Ibrahim-El-Khalil-Chaida/Real-Time-Embedded-System-for-Signal-Optimization-in-Battery-Analysis/Hardware/Images/Fritzing images/Current 2 pcb.JPG

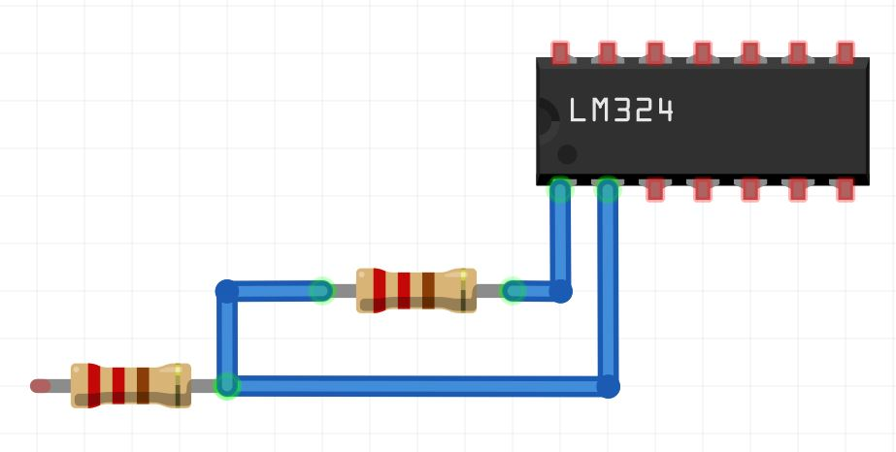
Hardware/Images/Fritzing images/Current 2 pcb.JPG
