Ibrahim-El-Khalil-Chaida/Real-Time-Embedded-System-for-Signal-Optimization-in-Battery-Analysis/Hardware/Images/Fritzing images/Full circuit.JPG

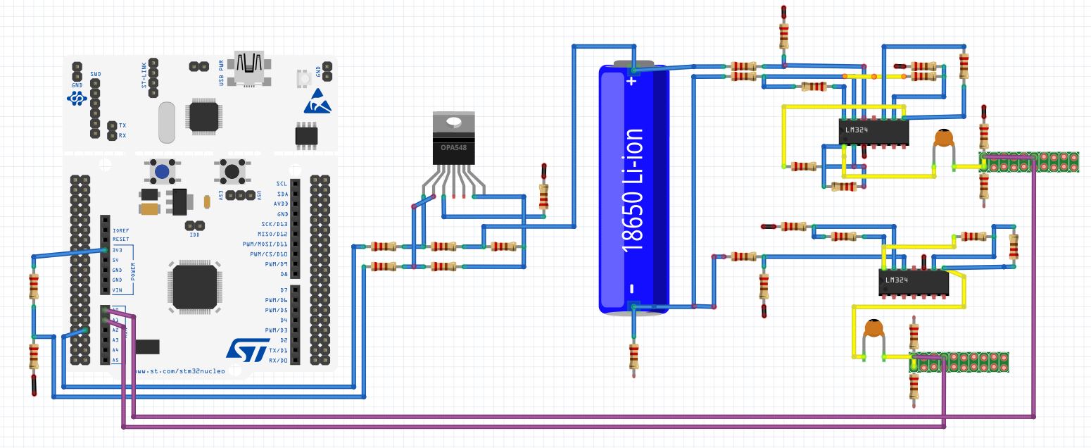
Hardware/Images/Fritzing images/Full circuit.JPG
