Ibrahim-El-Khalil-Chaida/Real-Time-Embedded-System-for-Signal-Optimization-in-Battery-Analysis/Hardware/Images/Fritzing images/Voltage 3 pcb.JPG

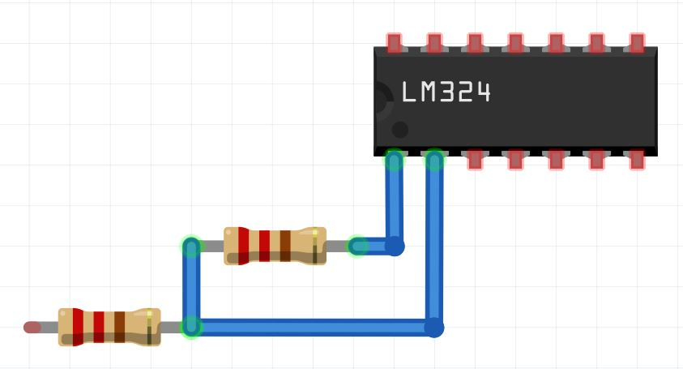
Hardware/Images/Fritzing images/Voltage 3 pcb.JPG
