Ibrahim-El-Khalil-Chaida/Real-Time-Embedded-System-for-Signal-Optimization-in-Battery-Analysis/Hardware/simulations/Measurment cicuit final.asc

C1: cap; 10µ
C3: cap; 10µ
R1: res; 10m
R2: res; 100k
R3: res; 100k
R4: res; 100k
R5: res; 100k
R6: res; 100k
R7: res; 100k
R8: res; 100k
R9: res; 100k
R10: res; 10k
R11: res; 10k
R12: res; 10k
R13: res; 10k
R14: res; 4
R15: res; 100k
R16: res; 33k
R17: res; 100k
R18: res; 100k
R19: res; 1k
R20: res; 600k
R21: res; 100k
R22: res; 100k
R23: res; 1k
R24: res; 60k
R25: res; 100k
R26: res; 100k
Rshunt: res; 100m
U1: ADA4522
U2: ADA4522
U3: OPA548
U4: ADA4522
U5: ADA4522
U6: ADA4522
V1: voltage; 3.7
V2: voltage; -12
V3: voltage; 12
V4: voltage; 1.65
V5: voltage; SINE(1.65 1 10)
V6: voltage; 3.7
V7: voltage; 3.3
Named nets: 0, vs+, vs-, bat-, bat+, volt_measur_1, curr_measur_1, volt_measur_2, volt_measur_3, volt_measur_4, curr_measur_2, vOffset, curr_measur_3
.tran 0 0.6 0.1 0.00001
* 1 = NON-INVERTING INPUT
* 2 = INVERTING INPUT
* 3 = CURRENT LIMIT
* 4 = NEGATIVE RAIL
* 5 = POSITIVE RAIL
* 6 = OUTPUT
* 7 = ENABLE/STATUS
